renezurbruegg/Demonstrator/3D Modelle/Case/preview.JPG

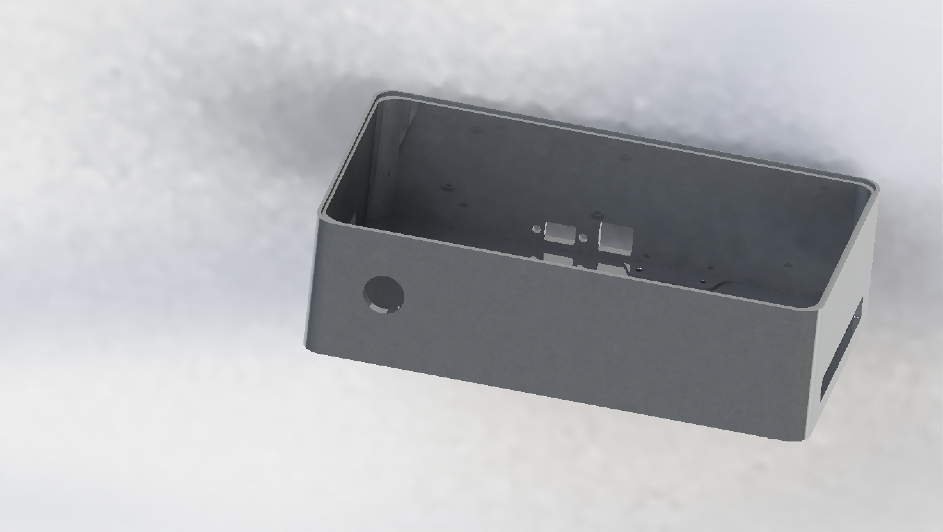
3D Modelle/Case/preview.JPG
