renezurbruegg/Demonstrator/3D Modelle/Case/Mechanical Drawings/Mechanical Drawing 12.PNG

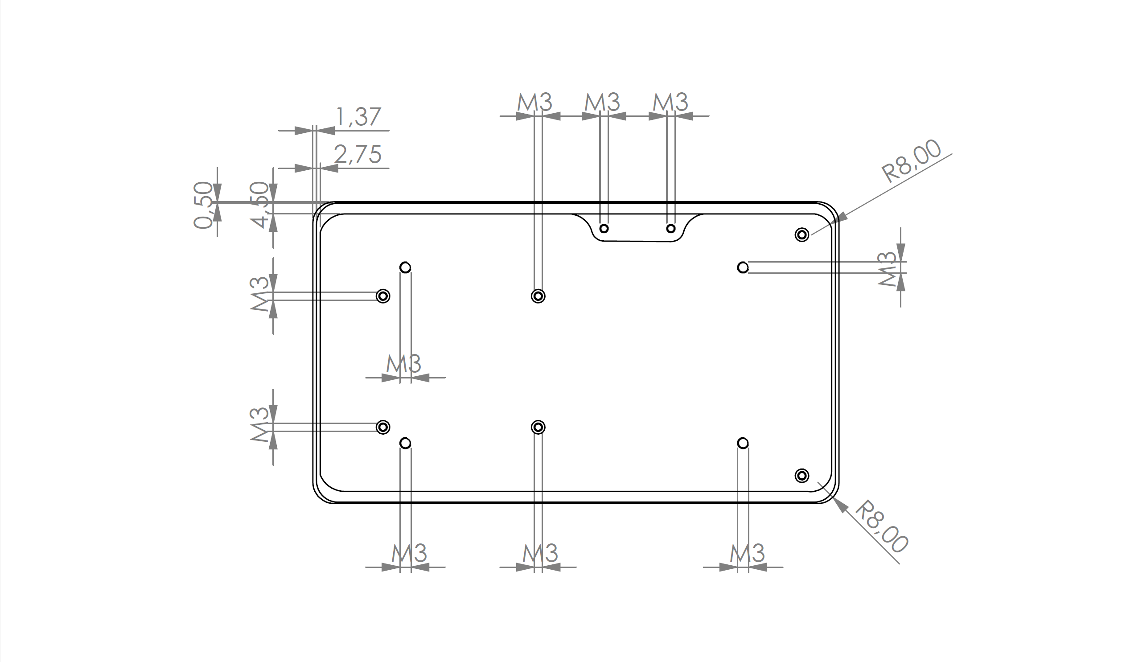
3D Modelle/Case/Mechanical Drawings/Mechanical Drawing 12.PNG
