renezurbruegg/Demonstrator/3D Modelle/Case/Mechanical Drawings/MechanicalDrawing5.PNG

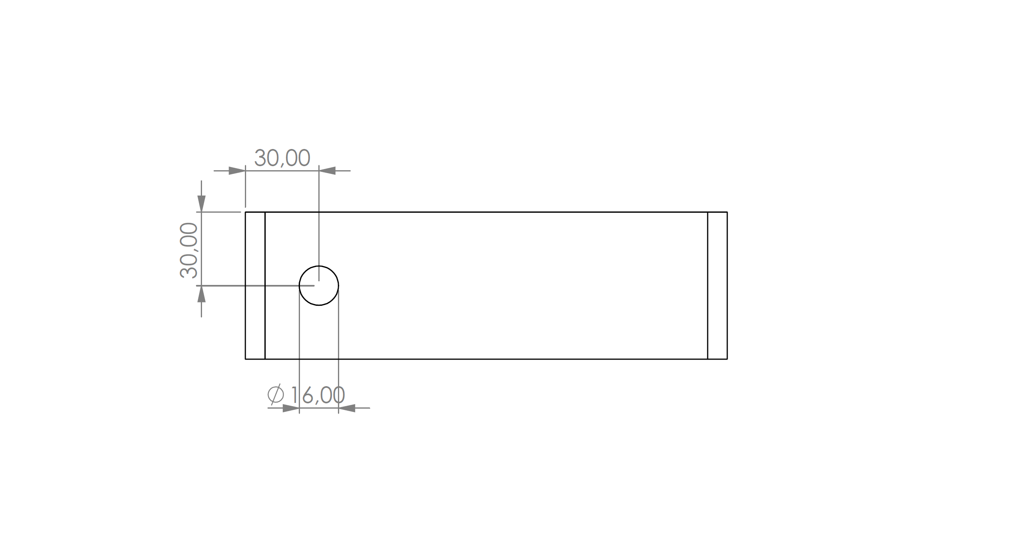
3D Modelle/Case/Mechanical Drawings/MechanicalDrawing5.PNG
