renezurbruegg/Demonstrator/3D Modelle/Case/preview2.JPG

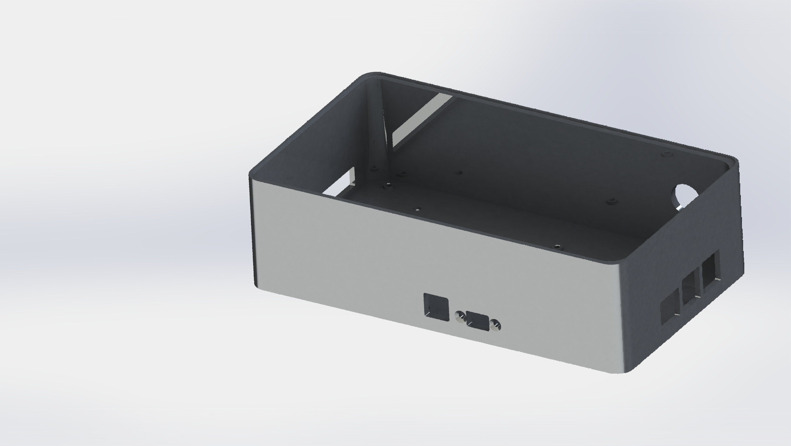
3D Modelle/Case/preview2.JPG
