renezurbruegg/Demonstrator/3D Modelle/Case/pulpdemonstrator.JPG

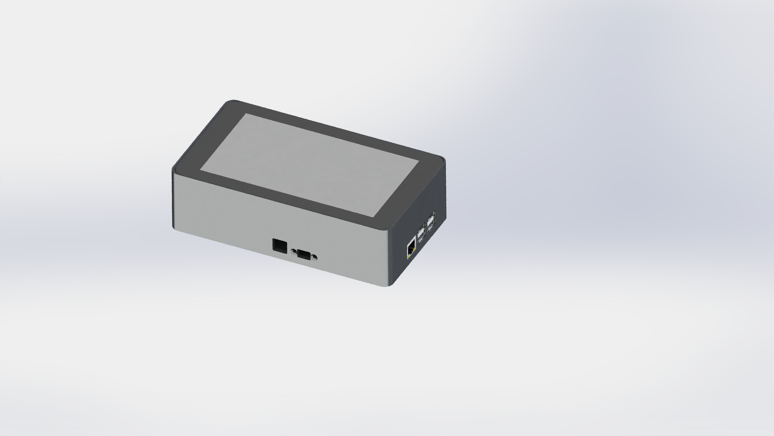
3D Modelle/Case/pulpdemonstrator.JPG
