renezurbruegg/Demonstrator/3D Modelle/Mount/halterunga.JPG

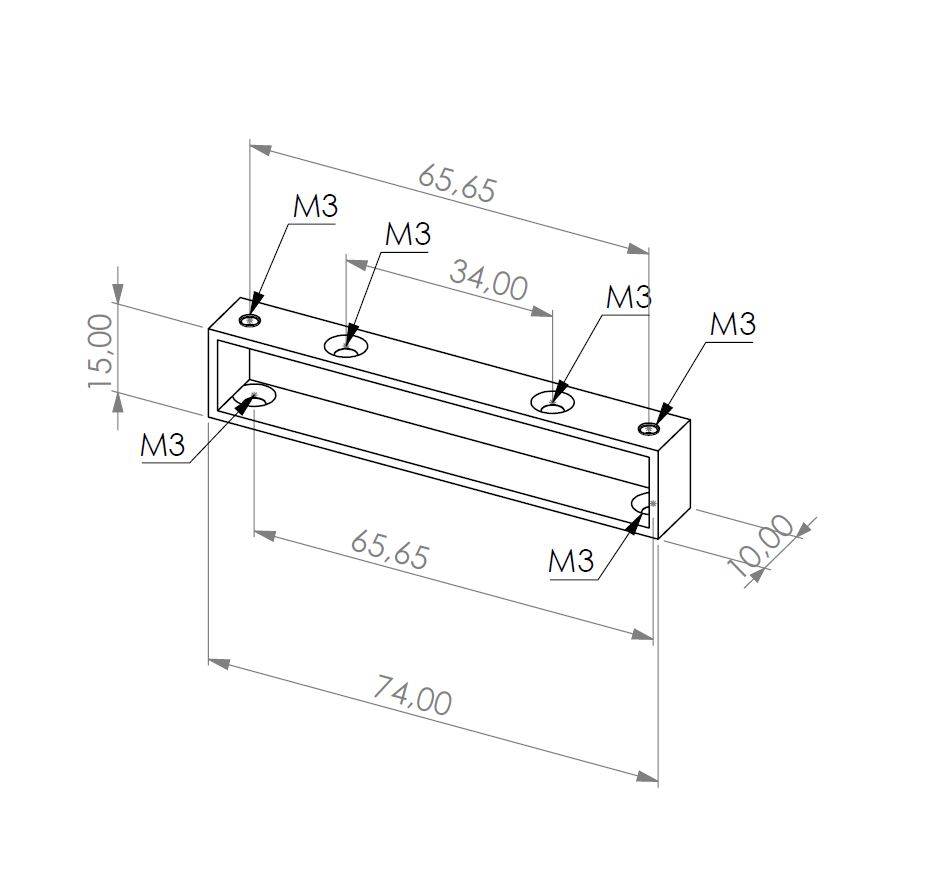
3D Modelle/Mount/halterunga.JPG
