renezurbruegg/Demonstrator/3D Modelle/Mount/halterungb.JPG

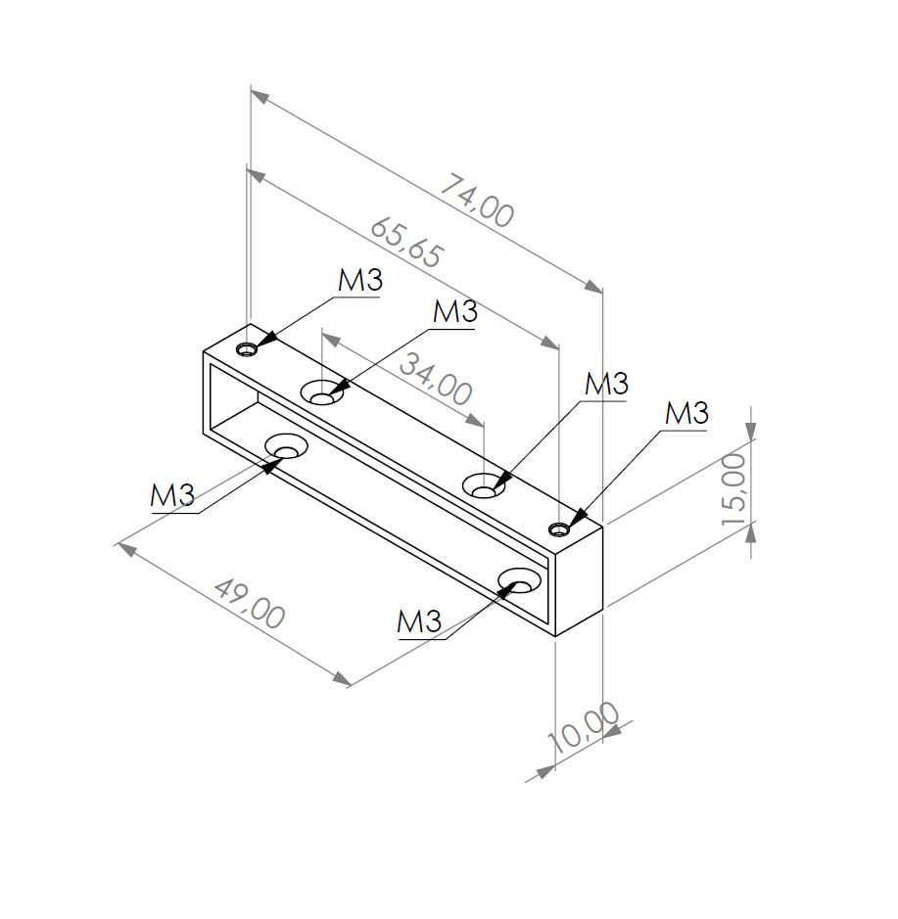
3D Modelle/Mount/halterungb.JPG
