renezurbruegg/Demonstrator/dokumentation/sources/negbodybias.jpg

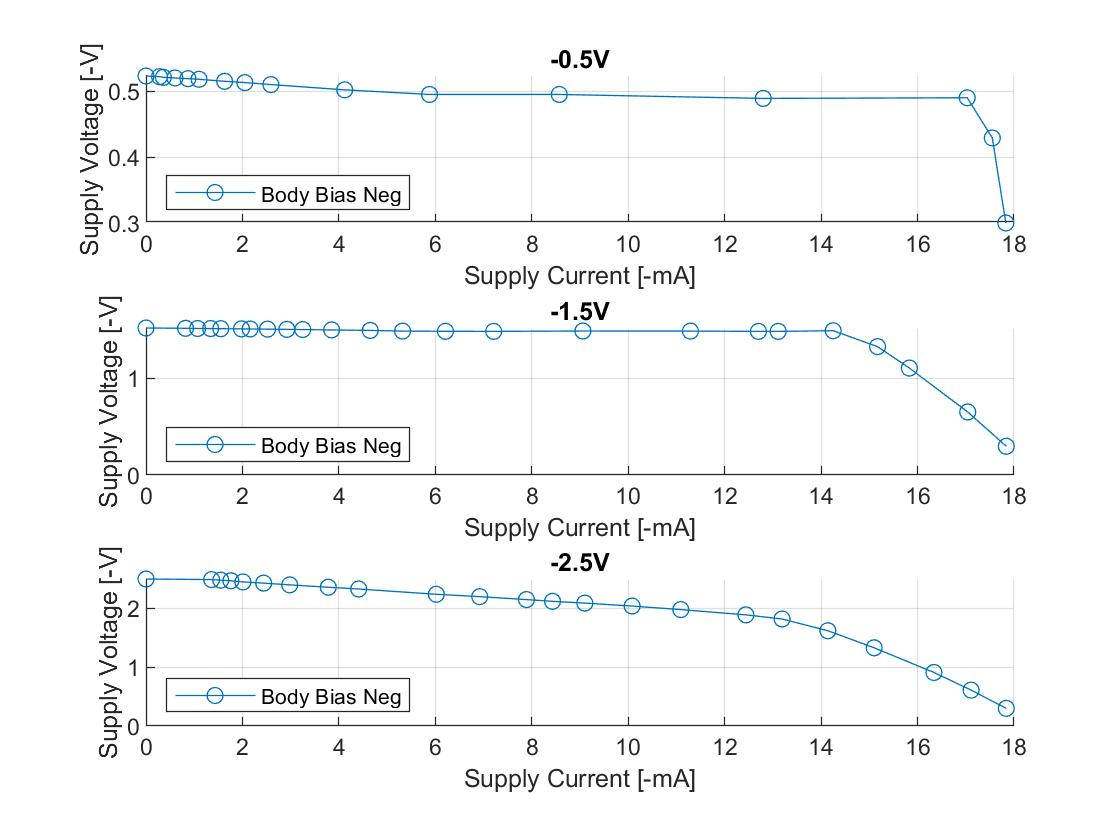
dokumentation/sources/negbodybias.jpg
