renezurbruegg/Demonstrator/dokumentation/sources/posbodybias.jpg

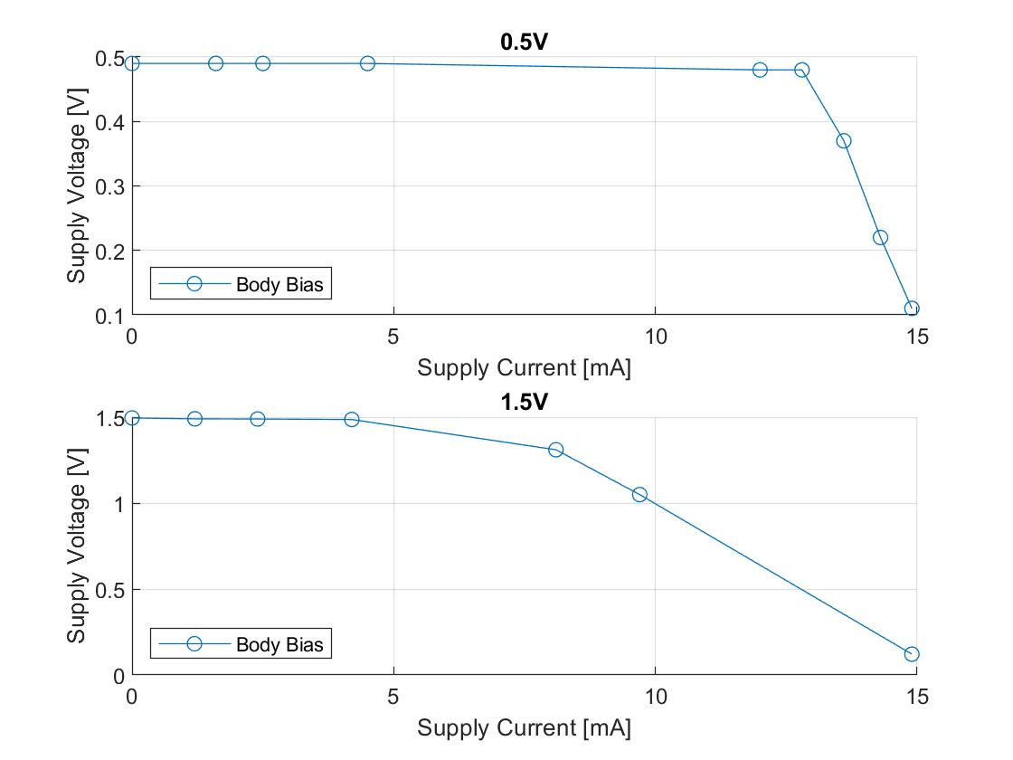
dokumentation/sources/posbodybias.jpg
