renezurbruegg/Demonstrator/dokumentation/sources/precisionall.jpg

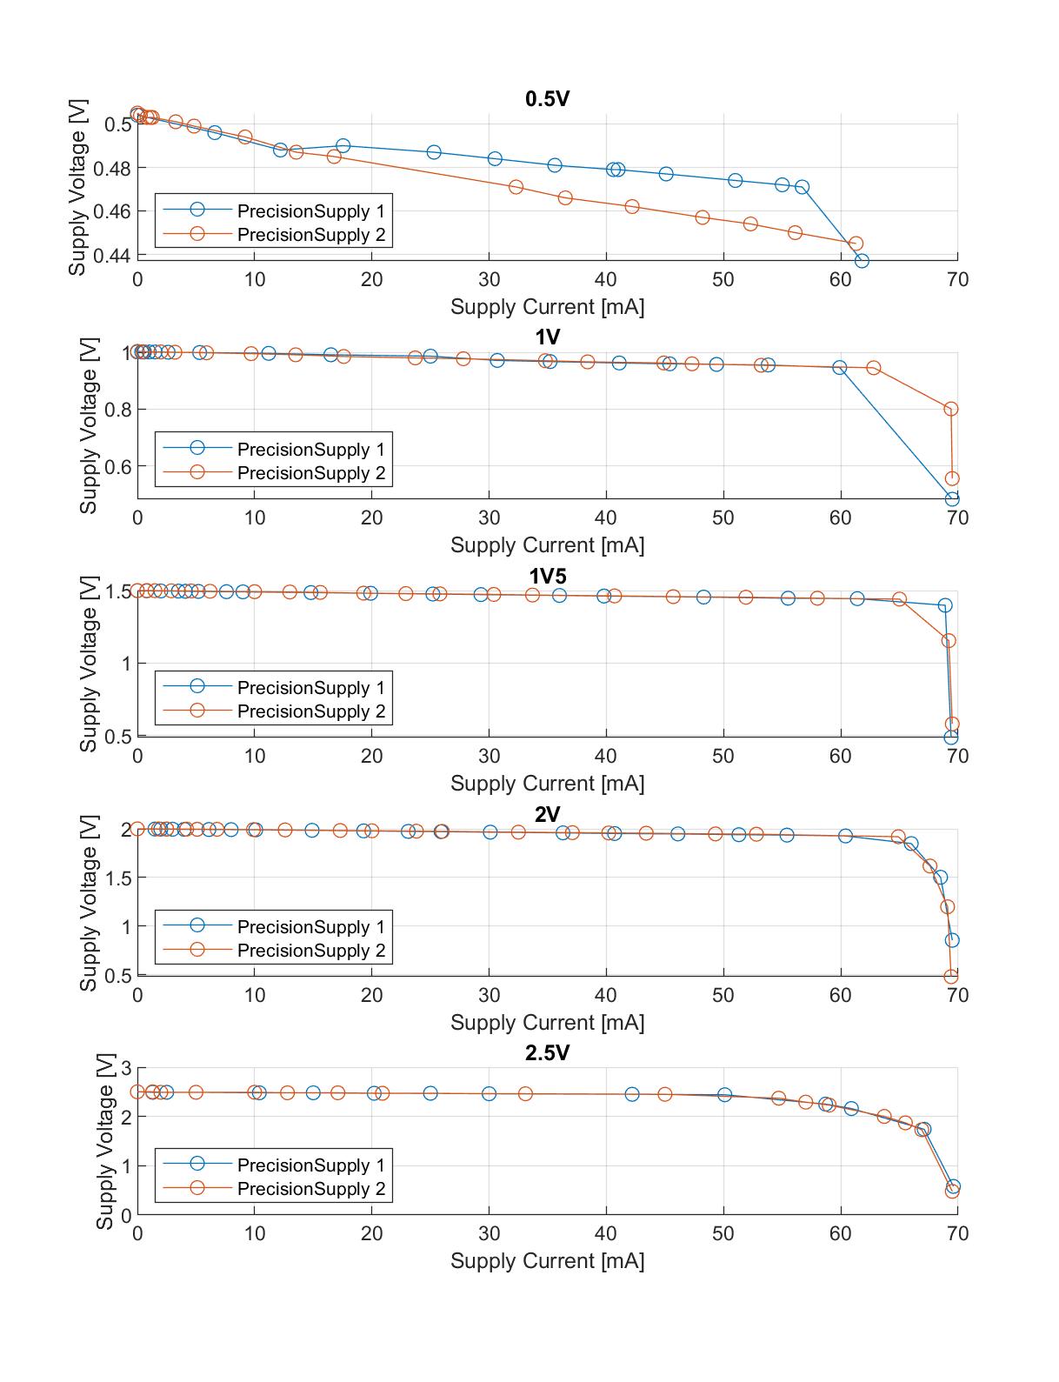
dokumentation/sources/precisionall.jpg
