renezurbruegg/Demonstrator/dokumentation/sources/PrecisionSupply0V.5.jpg

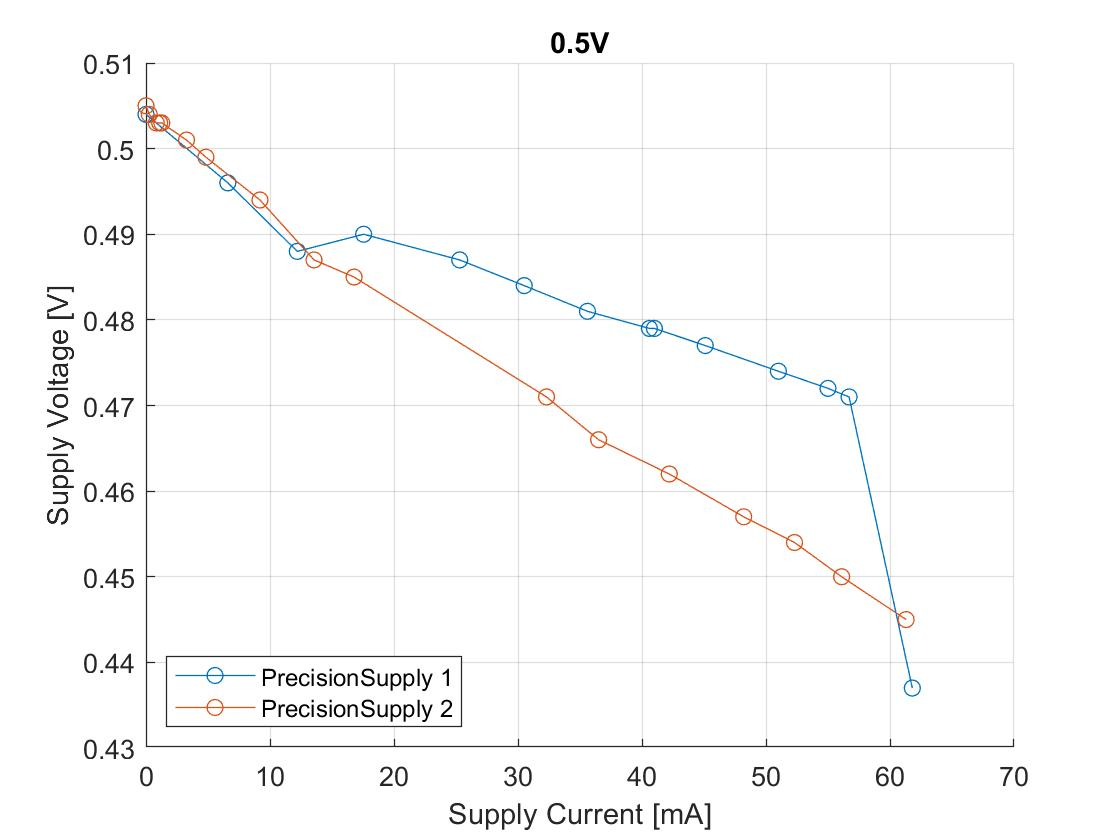
dokumentation/sources/PrecisionSupply0V.5.jpg
