renezurbruegg/Demonstrator/dokumentation/sources/PrecisionSupply1V.5jpg.jpg

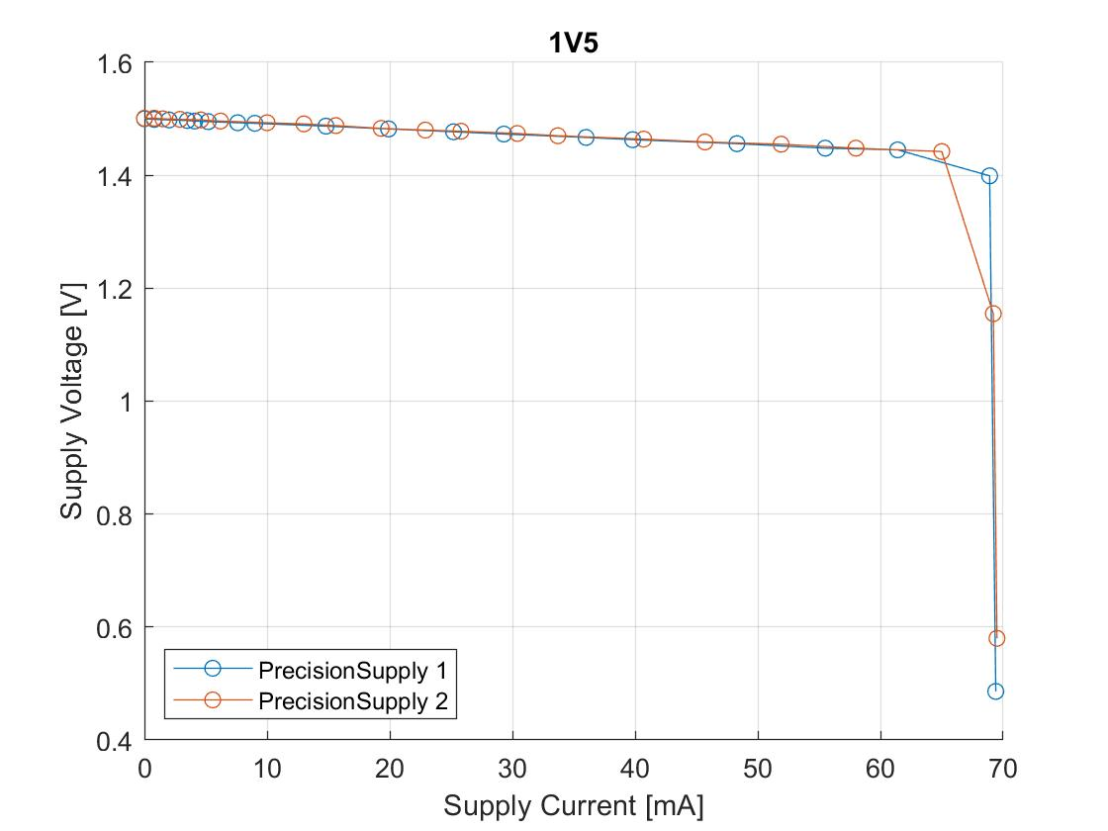
dokumentation/sources/PrecisionSupply1V.5jpg.jpg
