renezurbruegg/Demonstrator/dokumentation/sources/PrecisionSupply1V.jpg

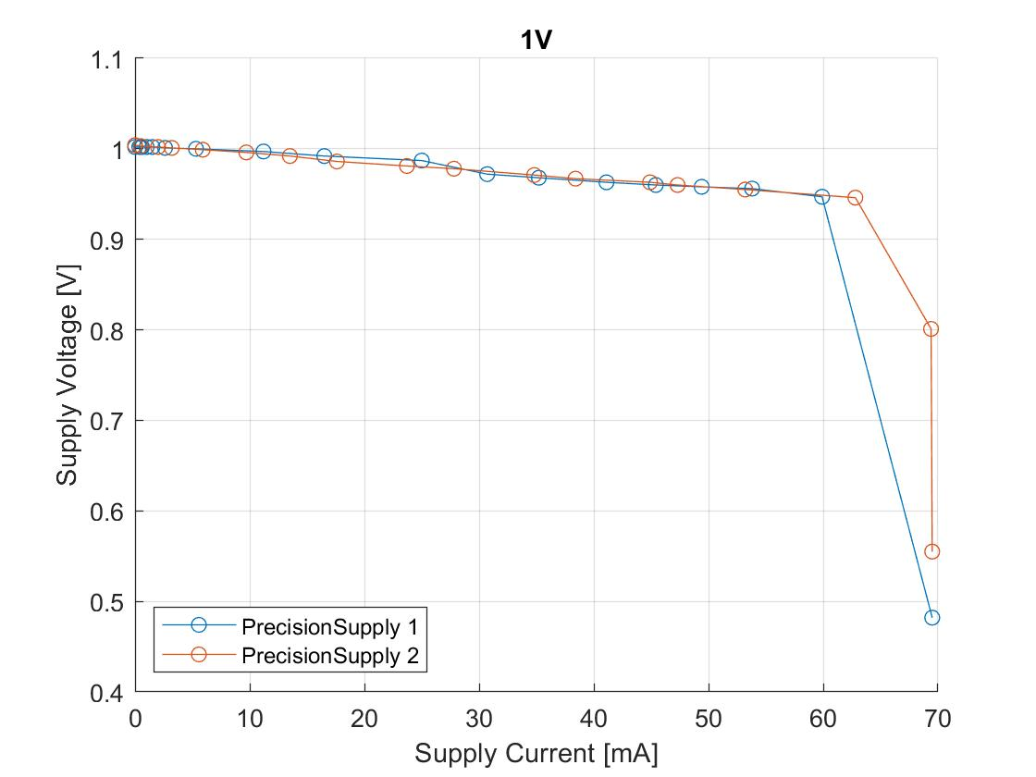
dokumentation/sources/PrecisionSupply1V.jpg
