renezurbruegg/Demonstrator/dokumentation/sources/PrecisionSupply2V5.jpg

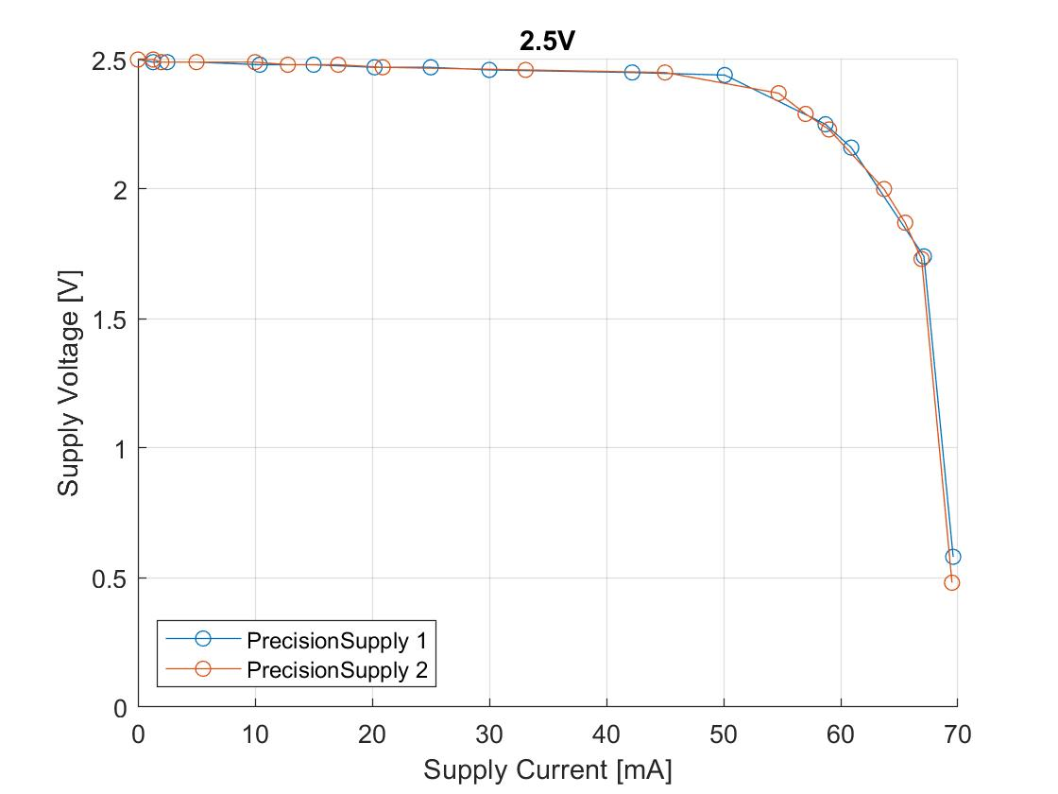
dokumentation/sources/PrecisionSupply2V5.jpg
