renezurbruegg/Demonstrator/dokumentation/sources/PrecisionSupply2V.jpg

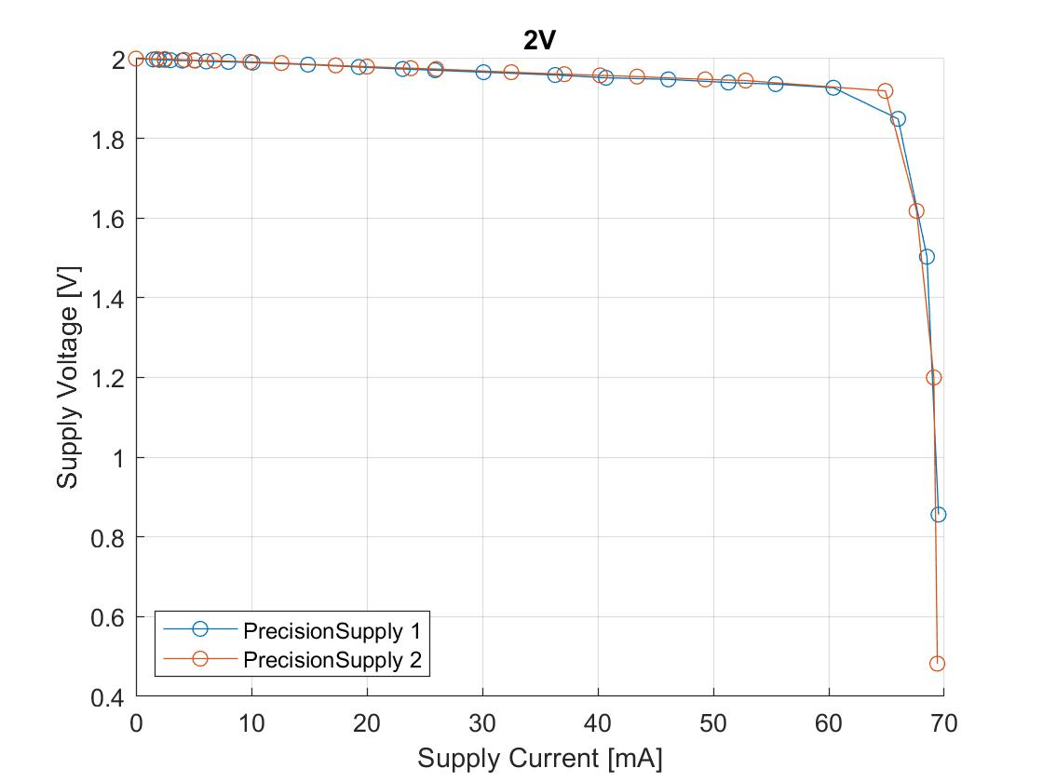
dokumentation/sources/PrecisionSupply2V.jpg
