renezurbruegg/Demonstrator/dokumentation/sources/precisionsupply.jpg

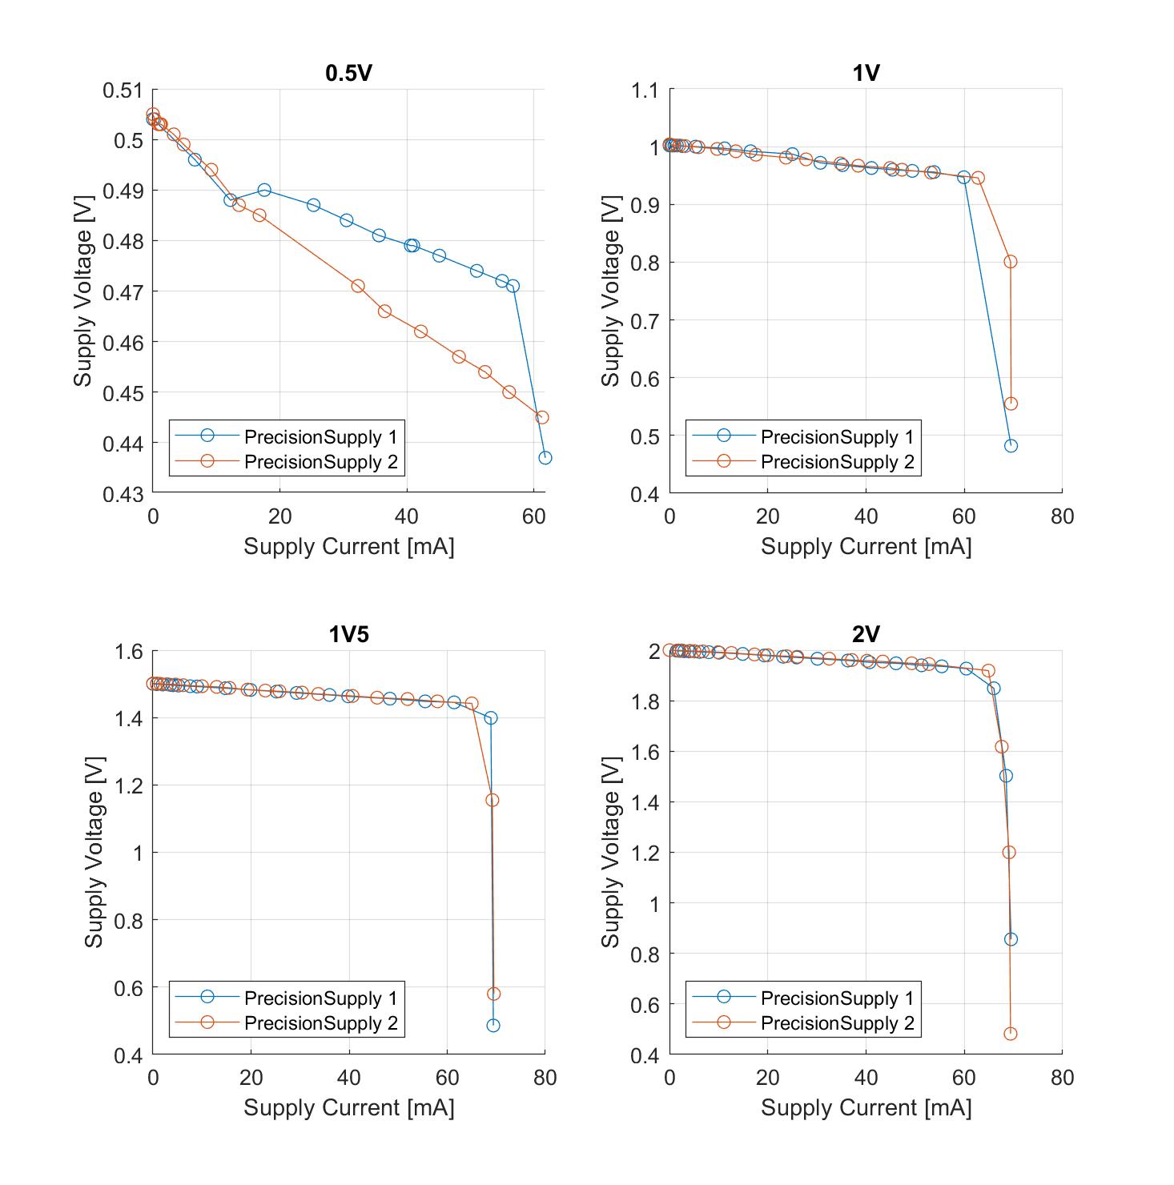
dokumentation/sources/precisionsupply.jpg
