renezurbruegg/Demonstrator/dokumentation/sources/untitled.jpg

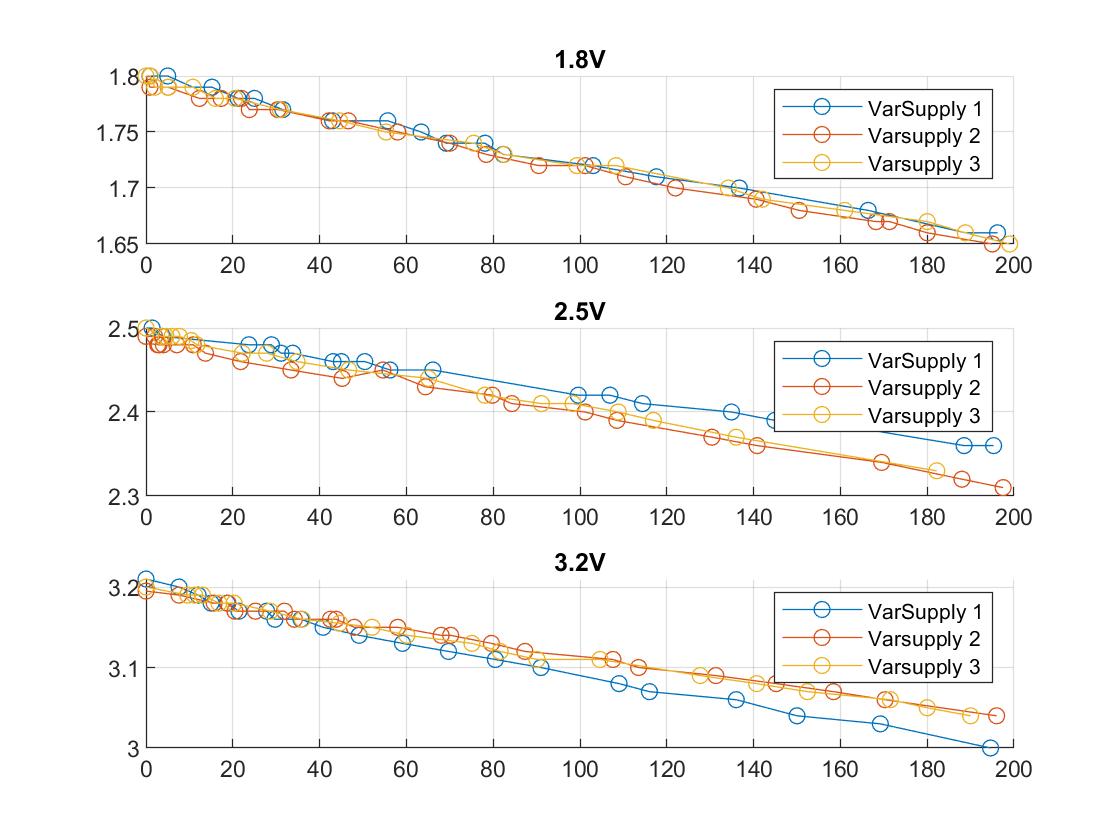
dokumentation/sources/untitled.jpg
