renezurbruegg/Demonstrator/dokumentation/sources/var.jpg

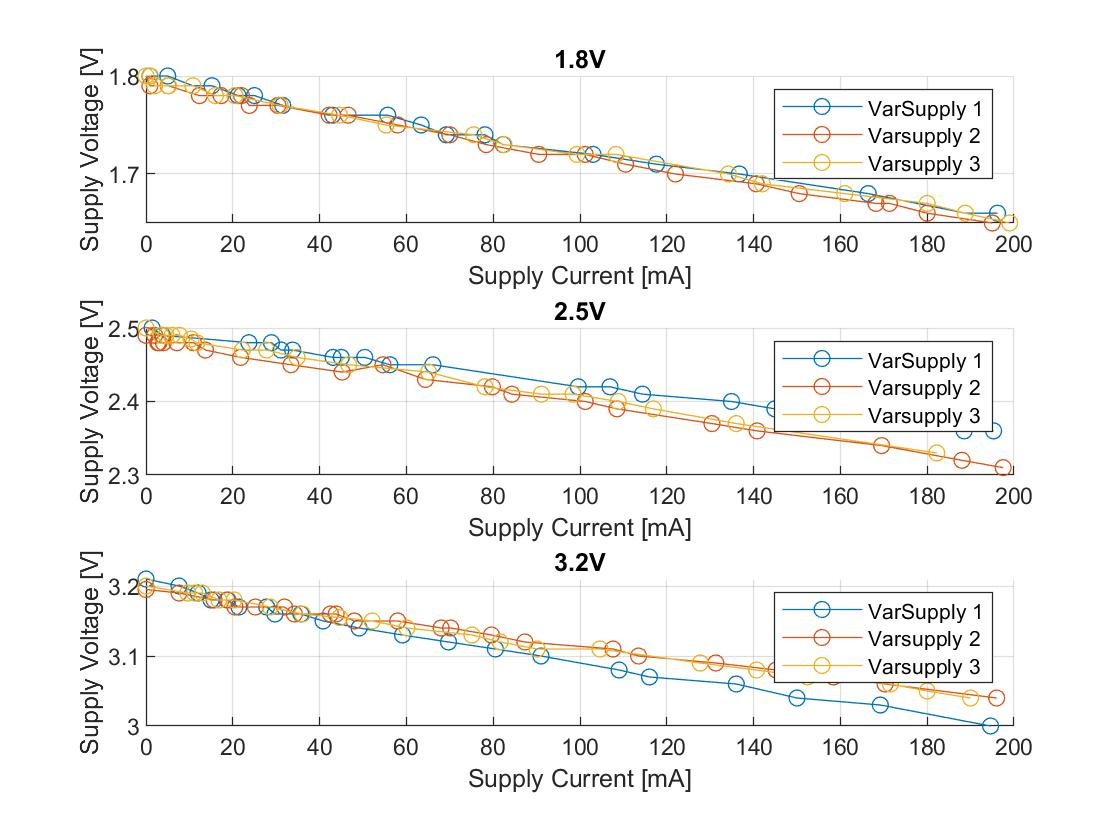
dokumentation/sources/var.jpg
