renezurbruegg/Demonstrator/dokumentation/transientResponse/precision1_2.5V_0.5mA_40mA.png

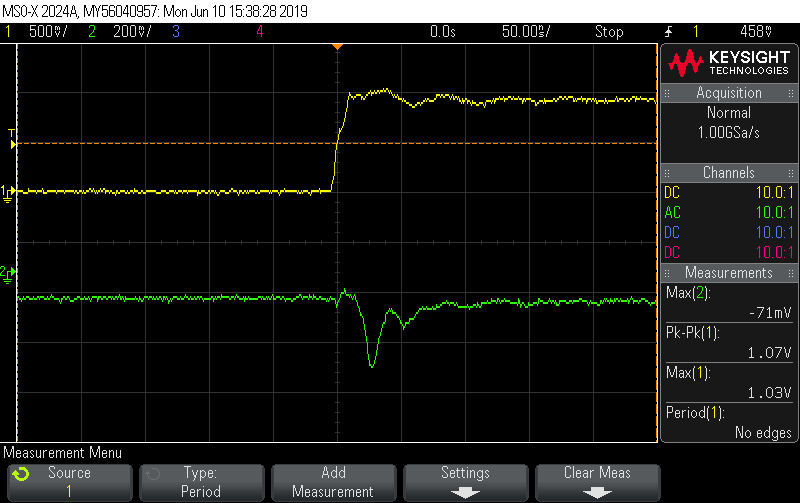
dokumentation/transientResponse/precision1_2.5V_0.5mA_40mA.png
