renezurbruegg/Demonstrator/dokumentation/transientResponse/precision1_2.5V_0.5mA_40mA_falling.png

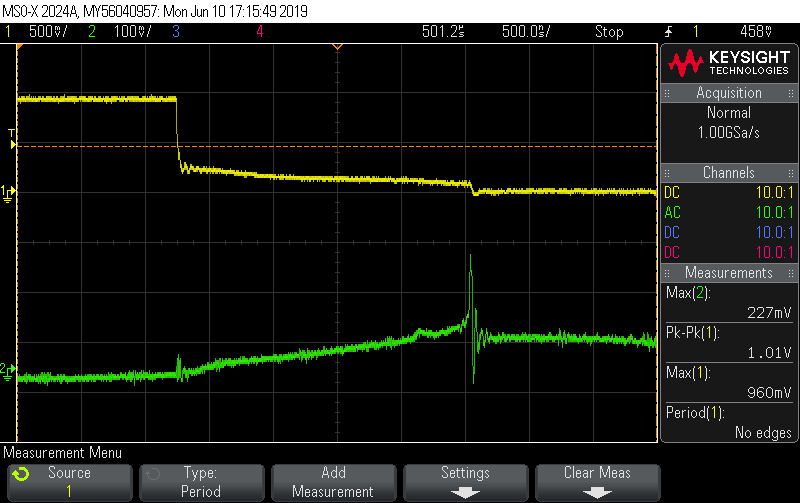
dokumentation/transientResponse/precision1_2.5V_0.5mA_40mA_falling.png
