renezurbruegg/Demonstrator/dokumentation/transientResponse/precision1_2.5V_10mA_40mA.png

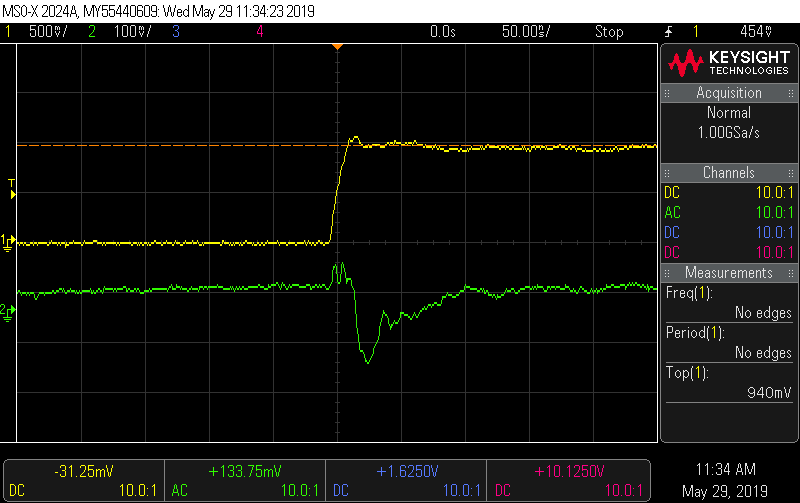
dokumentation/transientResponse/precision1_2.5V_10mA_40mA.png
