renezurbruegg/Demonstrator/dokumentation/transientResponse/precision2_2.5V_10mA_40mA.png

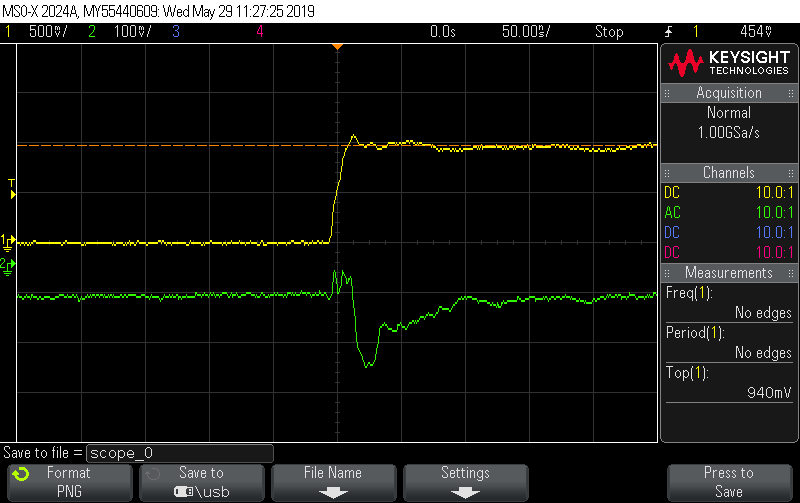
dokumentation/transientResponse/precision2_2.5V_10mA_40mA.png
