renezurbruegg/Demonstrator/dokumentation/transientResponse/PrecisionSupply1fallingedge05mA_40mA.png

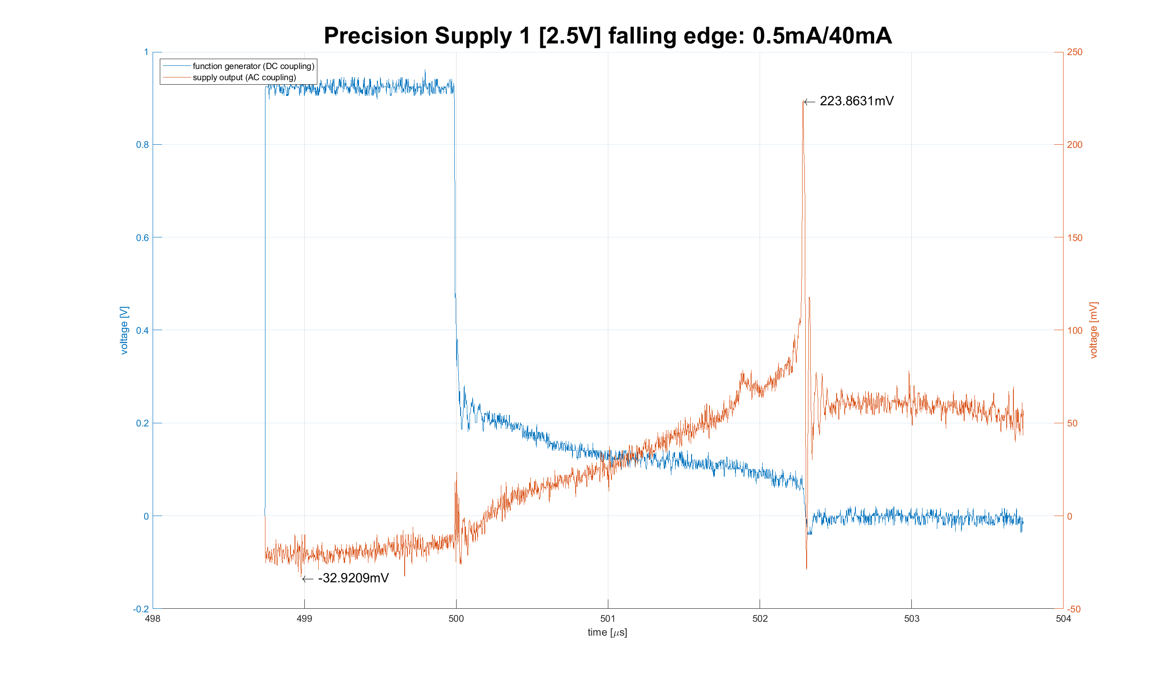
dokumentation/transientResponse/PrecisionSupply1fallingedge05mA_40mA.png
