renezurbruegg/Demonstrator/dokumentation/transientResponse/PrecisionSupply1risingedge05mA_40mA.png

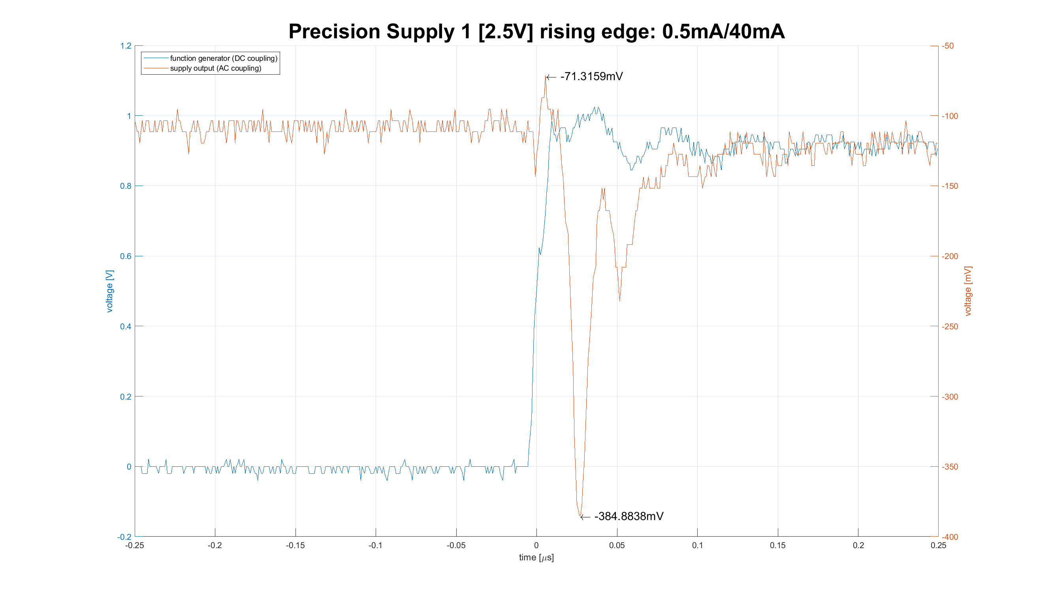
dokumentation/transientResponse/PrecisionSupply1risingedge05mA_40mA.png
