renezurbruegg/Demonstrator/dokumentation/transientResponse/PrecisionSupply1risingedge10mA_40mA.png

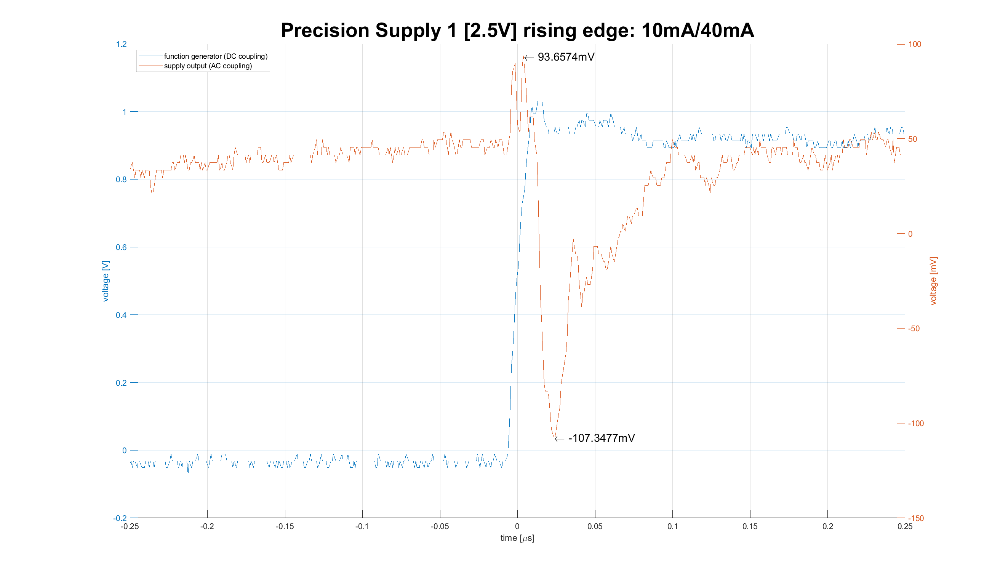
dokumentation/transientResponse/PrecisionSupply1risingedge10mA_40mA.png
