renezurbruegg/Demonstrator/dokumentation/transientResponse/PrecisionSupply2fallingedge05mA_40mA.png

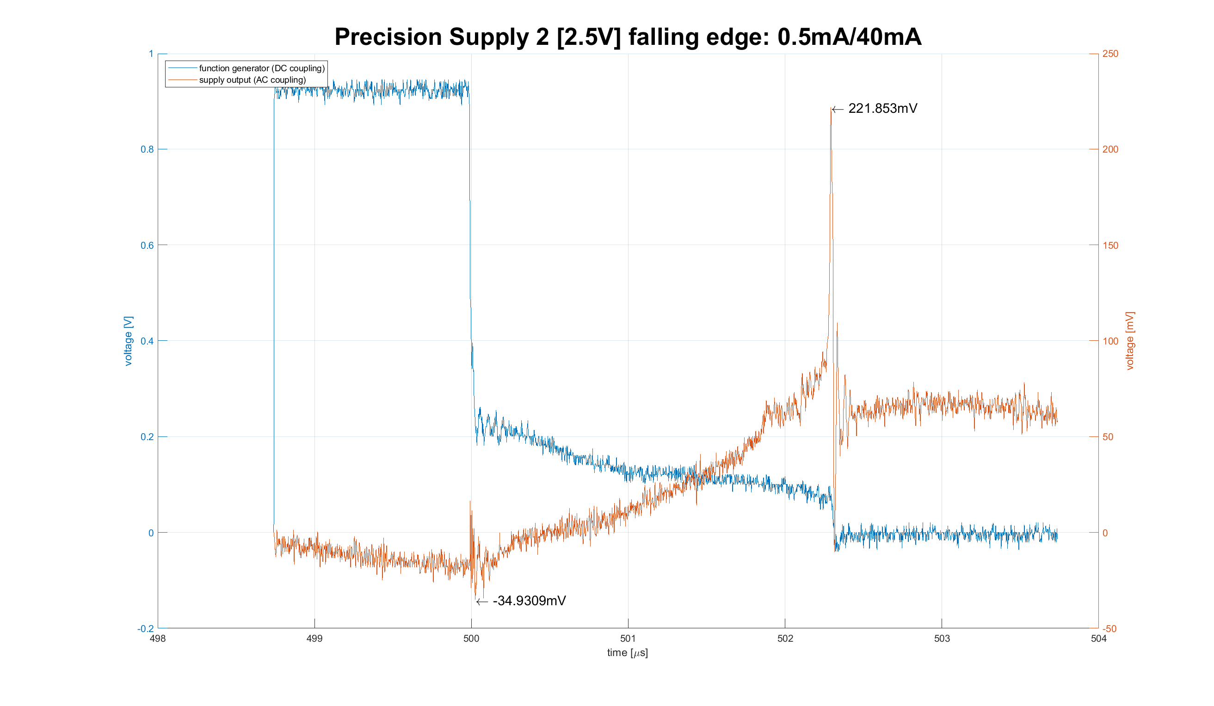
dokumentation/transientResponse/PrecisionSupply2fallingedge05mA_40mA.png
