renezurbruegg/Demonstrator/dokumentation/transientResponse/PrecisionSupply2risingedge05mA_40mA.png

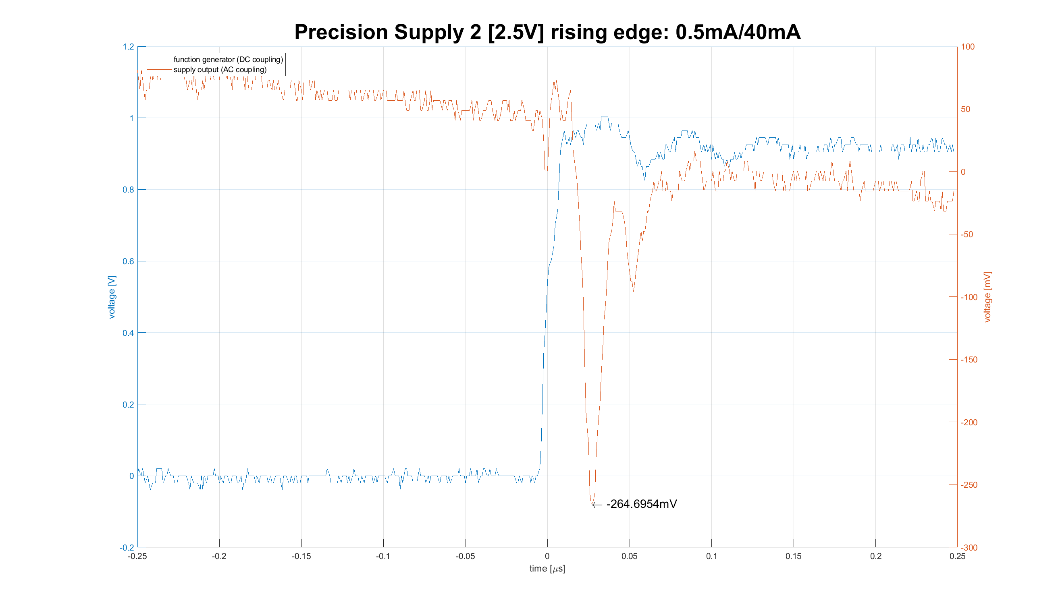
dokumentation/transientResponse/PrecisionSupply2risingedge05mA_40mA.png
