renezurbruegg/Demonstrator/dokumentation/transientResponse/PrecisionSupply2risingedge10mA_40mA.png

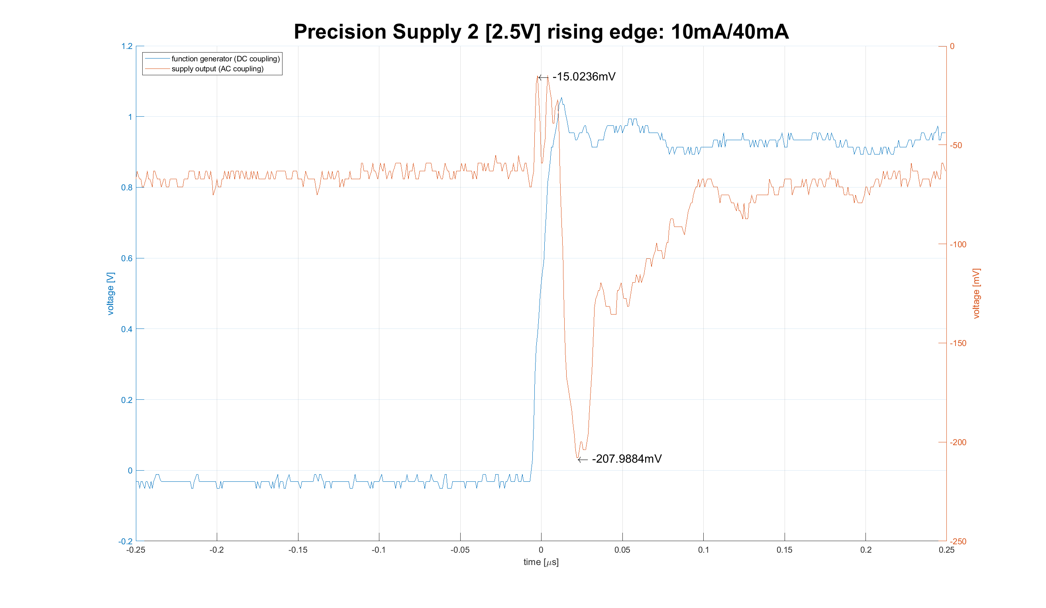
dokumentation/transientResponse/PrecisionSupply2risingedge10mA_40mA.png
