renezurbruegg/Demonstrator/dokumentation/transientResponse/var1_2.5V_0.5mA_100mA.png

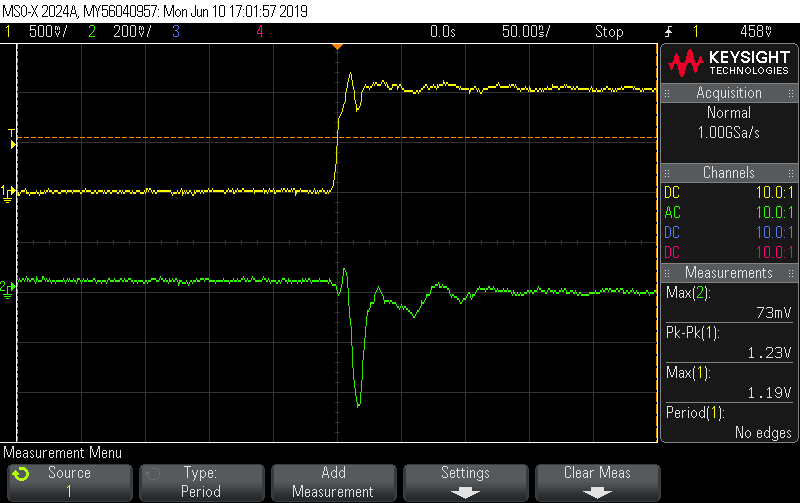
dokumentation/transientResponse/var1_2.5V_0.5mA_100mA.png
