renezurbruegg/Demonstrator/dokumentation/transientResponse/var1_2.5V_10mA_70mA.png

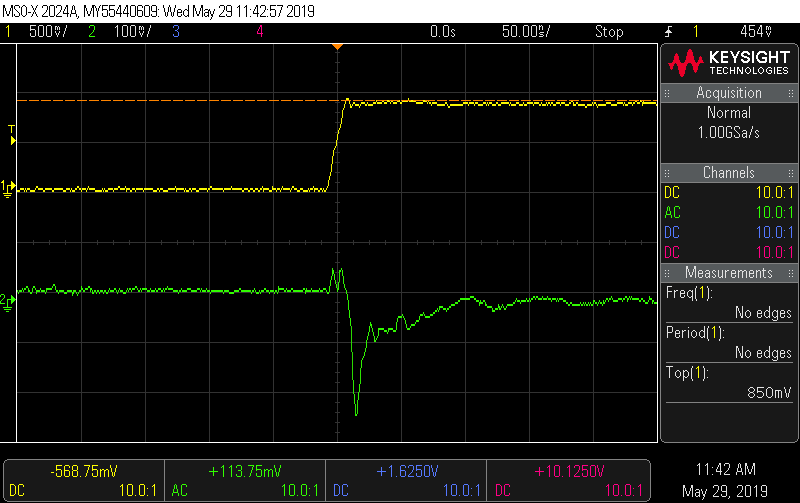
dokumentation/transientResponse/var1_2.5V_10mA_70mA.png
