renezurbruegg/Demonstrator/dokumentation/transientResponse/var2_2.5V_10mA_70mA_falling.png

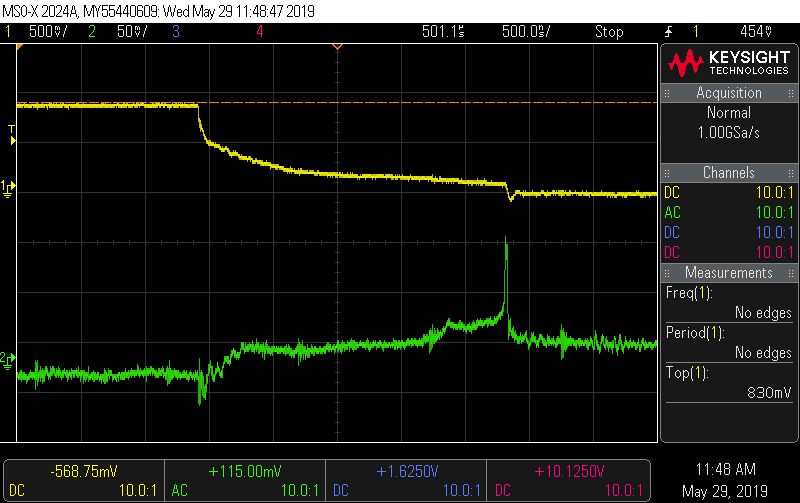
dokumentation/transientResponse/var2_2.5V_10mA_70mA_falling.png
