renezurbruegg/Demonstrator/dokumentation/transientResponse/var3_2.5V_10mA_70mA.png

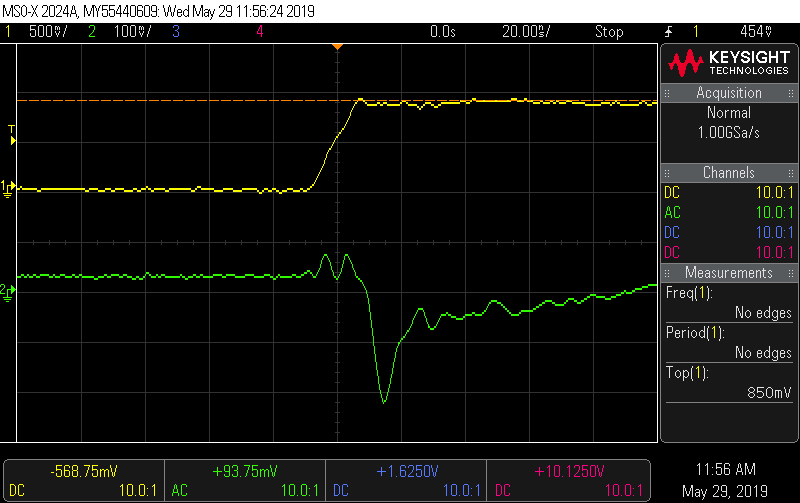
dokumentation/transientResponse/var3_2.5V_10mA_70mA.png
