renezurbruegg/Demonstrator/dokumentation/transientResponse/VariableSupply1fallingedge05mA_100mA.png

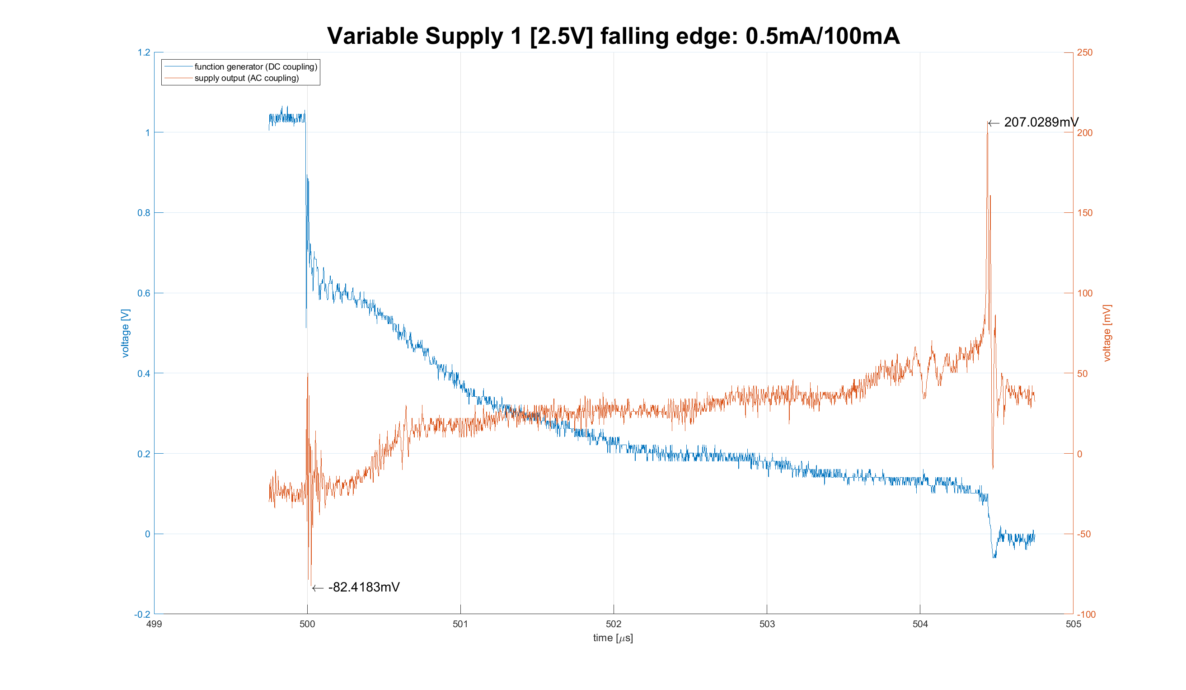
dokumentation/transientResponse/VariableSupply1fallingedge05mA_100mA.png
