renezurbruegg/Demonstrator/dokumentation/transientResponse/VariableSupply1fallingedge10mA_70mA.png

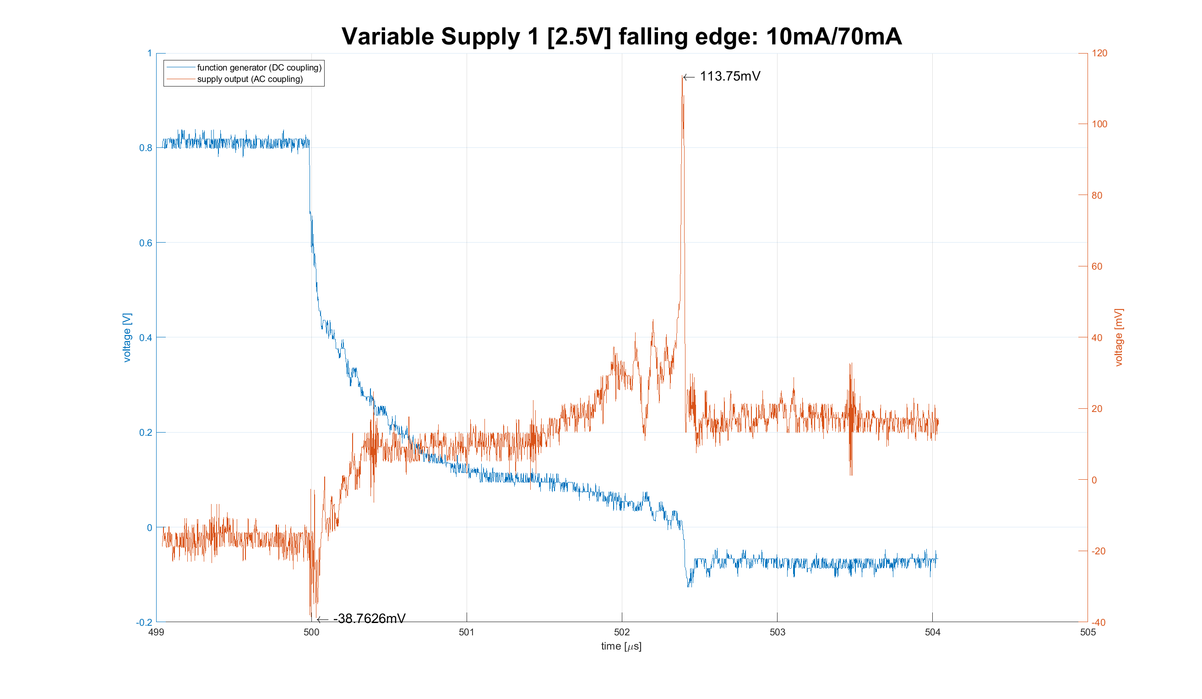
dokumentation/transientResponse/VariableSupply1fallingedge10mA_70mA.png
