renezurbruegg/Demonstrator/dokumentation/transientResponse/VariableSupply1risingedge05mA_100mA.png

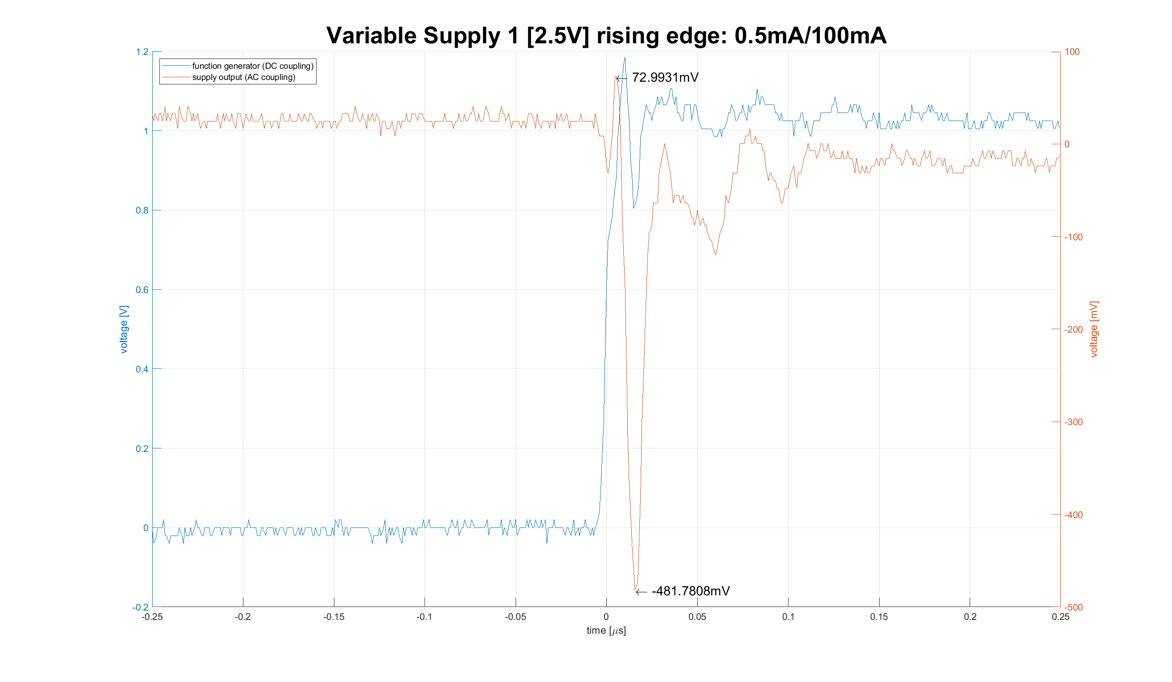
dokumentation/transientResponse/VariableSupply1risingedge05mA_100mA.png
