renezurbruegg/Demonstrator/dokumentation/transientResponse/VariableSupply1risingedge10mA_70mA.png

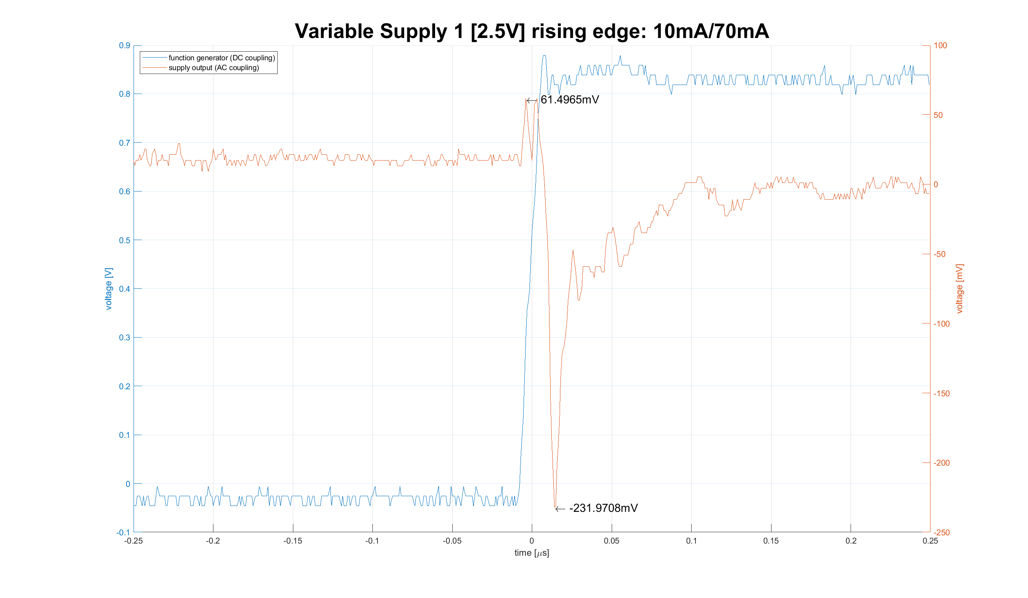
dokumentation/transientResponse/VariableSupply1risingedge10mA_70mA.png
