renezurbruegg/Demonstrator/dokumentation/transientResponse/VariableSupply2fallingedge10mA_70mA.png

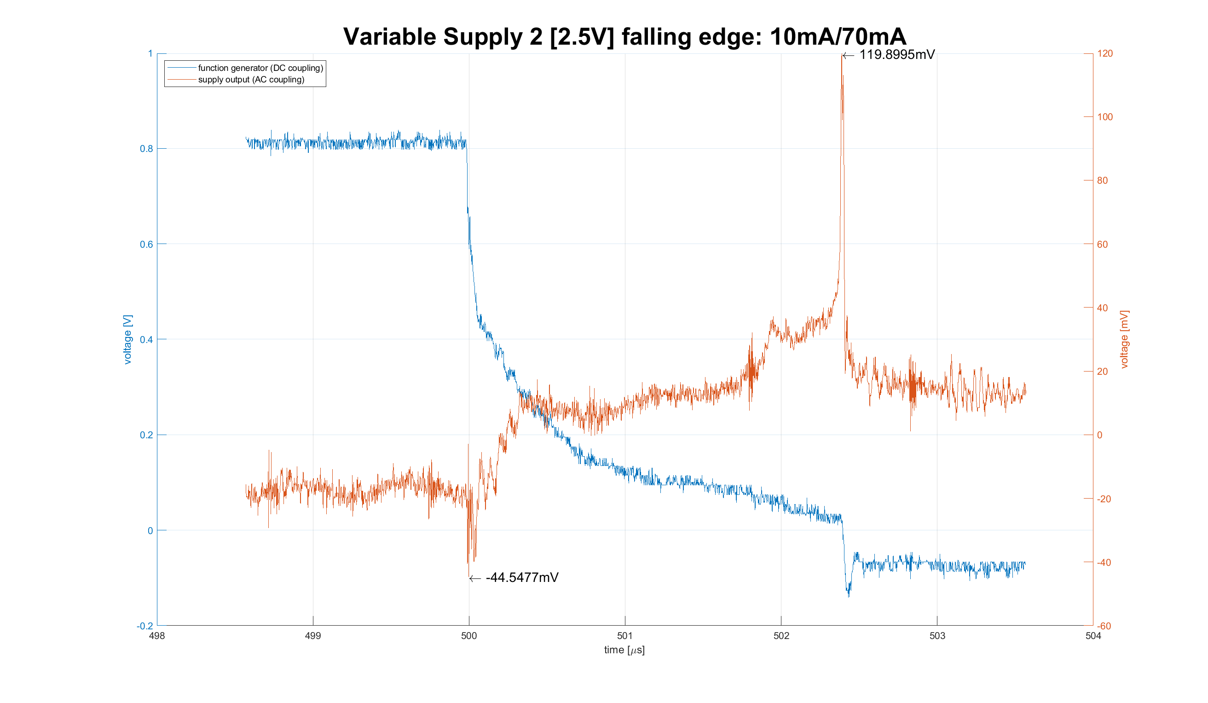
dokumentation/transientResponse/VariableSupply2fallingedge10mA_70mA.png
