renezurbruegg/Demonstrator/dokumentation/transientResponse/VariableSupply2risingedge05mA_100mA.png

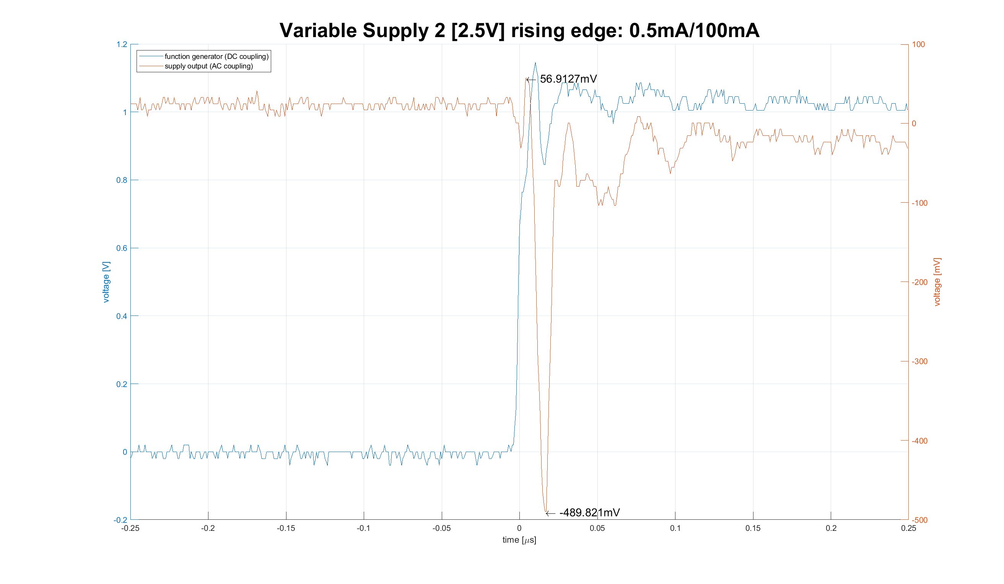
dokumentation/transientResponse/VariableSupply2risingedge05mA_100mA.png
