renezurbruegg/Demonstrator/dokumentation/transientResponse/VariableSupply2risingedge10mA_70mA.png

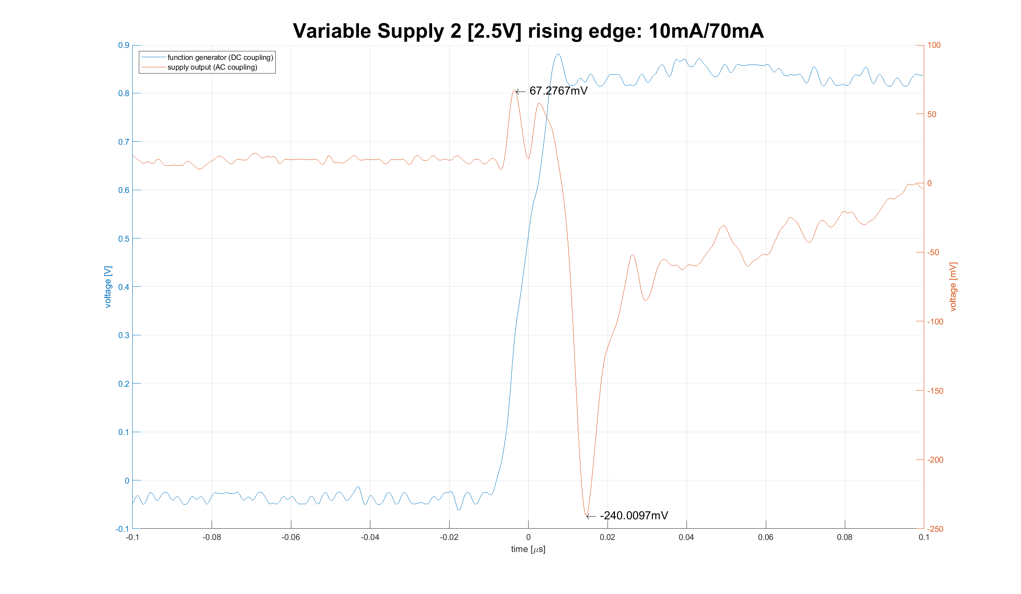
dokumentation/transientResponse/VariableSupply2risingedge10mA_70mA.png
