renezurbruegg/Demonstrator/dokumentation/transientResponse/VariableSupply3fallingedge10mA_70mA.png

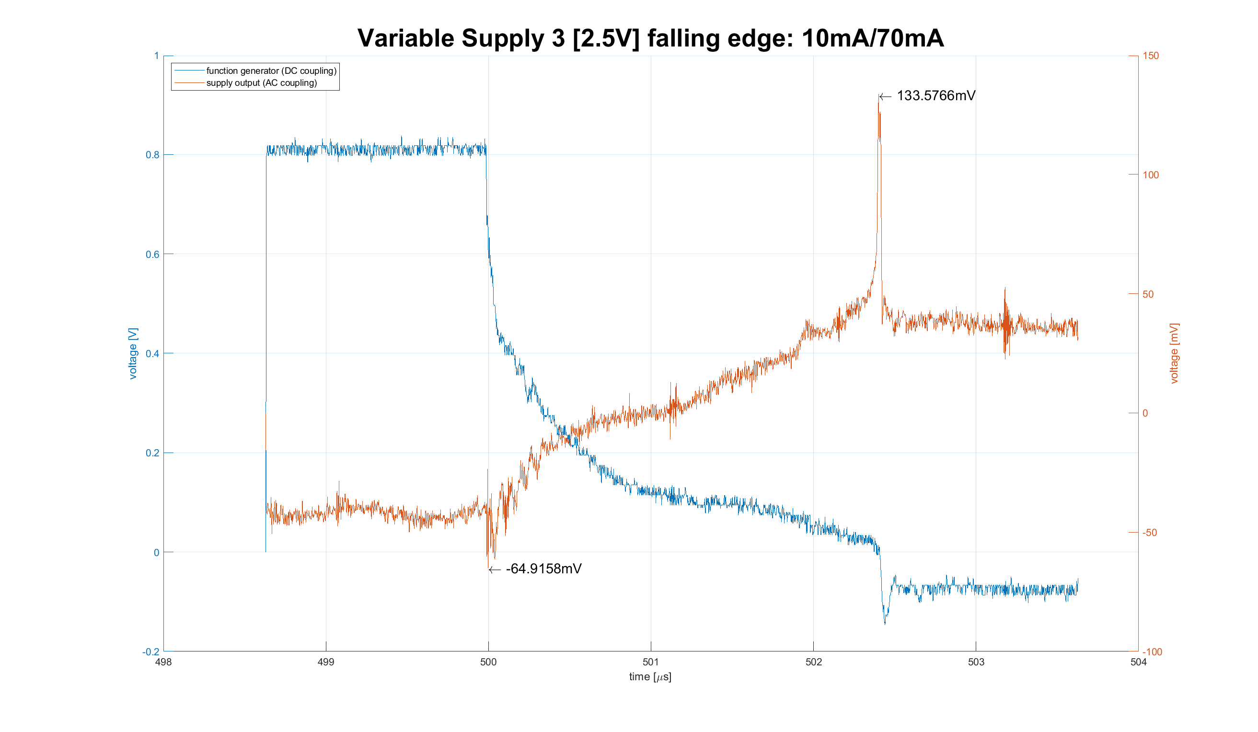
dokumentation/transientResponse/VariableSupply3fallingedge10mA_70mA.png
