renezurbruegg/Demonstrator/dokumentation/transientResponse/VariableSupply3risingedge05mA_100mA.png

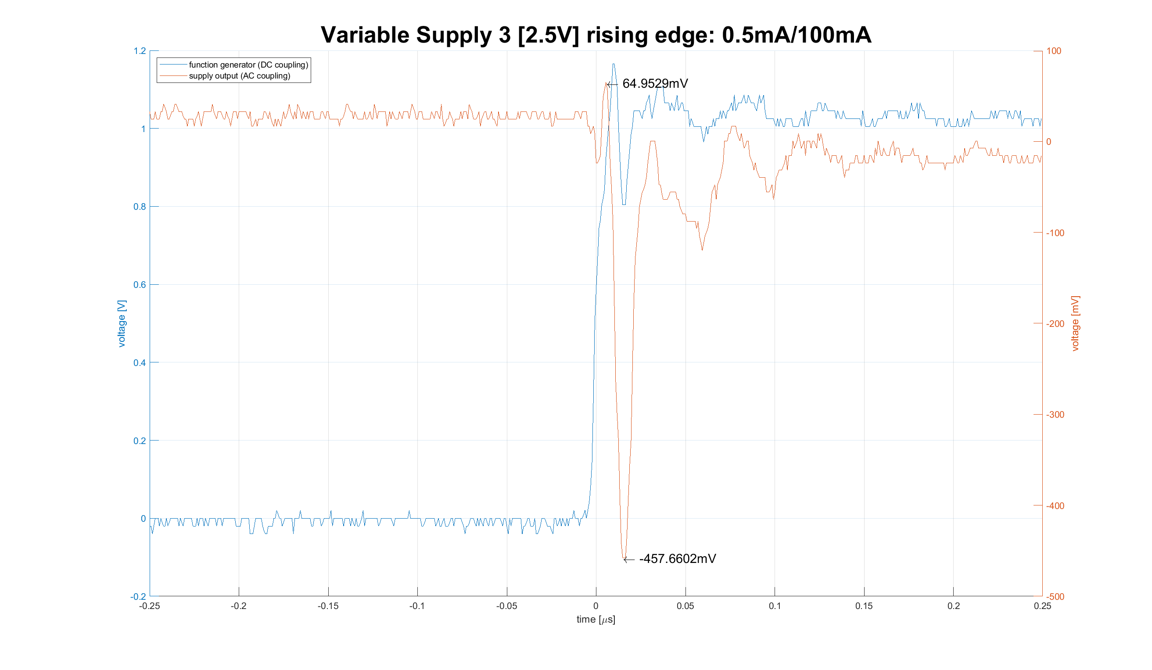
dokumentation/transientResponse/VariableSupply3risingedge05mA_100mA.png
