renezurbruegg/Demonstrator/dokumentation/measurements/current/meas_CM3_19.9994_mA.csv

cm3
20.533077261233988
20.68565029035561
20.53222010938499
20.608506623945804
20.582792068475865
20.41221885052529
20.359075435887423
20.747365223483456
20.44307631708921
20.60593516839881
20.49364827618009
20.624792509076762
20.372789865471386
20.555363209307934
20.501362642821068
20.399361572790323
20.591363586965844
20.49364827618009
20.643649849754716
20.78679420853736
20.546791690817955
20.399361572790323
20.53222010938499
20.604220864700814
20.4885053650861
20.58107776477787
20.675364468167636
20.72165066801352
20.258788669554672
20.622221053529767
20.680507379261623
20.517648527952026
20.619649597982775
20.32393221007851
20.511648465009042
20.554506057458937
20.567363335193903
20.606792320247806
20.426790431958253
20.620506749831772
20.46793372071015
20.341075247058466
20.508219857613053
20.4885053650861
20.528791501989
20.539934476025973
20.662507190432667
20.682221682959618
20.74993667903045
20.52450574274401
20.689078897751603
20.662507190432667
20.4893625169351
20.577649157381877
20.413933154223287
20.648792760848703
20.457647898522175
20.691650353298595
20.385647143206356
20.382218535810363
20.527077198291003
20.337646639662474
20.665078645979662
20.515934224254032
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
