renezurbruegg/Demonstrator/dokumentation/measurements/current/meas_CM3_199.996_uA.csv

cm3
203.26561688336858
195.48580357989184
204.7205670783011
196.7044402081315
188.96632929877697
200.85614522297078
197.94161123375883
204.6232614920158
200.97661880599068
205.95310450458152
199.14634706395773
196.9314865761305
200.5688620634618
202.12111784467962
204.70203268091342
198.71078872534736
193.4840886620229
195.0039092478123
199.3131566404468
203.13587610165484
200.38815168893197
197.55702248796456
196.95928817221204
204.33597833250684
200.04526533726
201.7457962975792
203.64557202981592
201.1758635779082
206.91689316874064
198.83126230836726
198.60421594036822
202.13501864272038
198.92856789465253
195.03634444324072
207.8714146342059
202.20452263292415
203.66874002655052
201.643857111947
200.72640444125705
201.300970760275
189.08680288179687
207.56096347796236
198.68762072861276
203.6872744239382
196.94075377482437
196.4588594427448
200.97661880599068
199.13244626591697
196.19011068062352
201.33803955505033
196.2318130747458
194.46177812422277
198.90539989791796
201.92650667210904
202.51497378916773
205.31830139405363
201.3241387570096
202.19062183488342
199.44289742216054
194.08182297777543
203.09417370753258
201.56508592304937
193.29411108879924
200.60593085823717
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
