renezurbruegg/Demonstrator/dokumentation/measurements/current/meas_CM3_299.994_uA.csv

cm3
288.6860208438174
301.7203358067002
295.7985958413379
297.5639971925139
296.86432369112924
287.9261105509227
301.70643500865935
302.1327261485759
307.79961814985774
294.37608084183375
306.6782871079034
302.1651613440044
300.0059040483402
300.4090271915221
296.3824293590497
307.4196630034104
306.82192868765776
292.85162665669753
302.5960860832678
299.84372807119803
303.4069659689786
300.6314399601742
302.55901728849244
302.415375708738
305.10286332995094
293.565200956123
303.0733468160005
297.59179878859544
293.5188649626538
298.5046178599385
290.8174765434001
294.52435602093516
291.9341739860076
289.2096175700193
302.46634530155404
301.3913502530689
299.99200325029943
311.53893282282115
290.50239178780964
295.4510758903189
300.79824953666326
298.6853282344683
305.895208818274
302.84166684865454
300.6777759536434
295.13599113472844
298.16173150826654
293.5559337574292
297.2906148310458
300.6916767516842
291.52641724347876
295.3537703040337
294.81163918044416
300.4970655791136
307.2343190295336
293.3010857933486
297.2998820297396
292.64774828543307
304.83411456782966
306.14078958366076
307.9942293224283
299.8576288692388
307.5679381825118
305.54768886725515
292.1287851585782
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
