renezurbruegg/Demonstrator/dokumentation/measurements/current/meas_CM3_30.0003_mA.csv

cm3
30.921757671088187
30.88061438233629
30.77175609751356
30.966329567236077
30.776899008607547
30.842042549131385
30.870328560148316
30.746041542043624
30.769184641966564
30.810327930718465
30.668897875633814
30.974043933877056
31.01690152632695
30.986901211612025
31.01690152632695
30.78289907155053
31.016044374477953
30.866042800903326
30.850614067621365
30.721184138422686
30.794042045587503
30.82747096769842
30.904614634108228
30.92518627848418
30.986901211612025
30.790613438191514
30.89261450822226
30.793184893738506
31.039187474400894
30.666326420086822
30.844614004678377
30.851471219470362
30.90032887486324
30.88061438233629
30.750327301288614
30.85918558611134
30.842042549131385
30.933757796974156
30.772613249362557
30.753755908684603
30.918329063692195
30.861757041658336
30.893471660071256
30.830899575094413
30.983472604216033
30.974043933877056
30.993758426404007
30.935472100672154
30.84804261207437
30.656040597898848
30.987758363461023
30.74347008649663
30.701469645895735
30.86347134535633
30.7151840754797
30.753755908684603
30.76747033826857
30.500038961381236
30.967186719085074
30.85918558611134
30.981758300518038
30.90032887486324
30.96804387093407
30.890043052675267
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
