renezurbruegg/Demonstrator/dokumentation/measurements/voltage/voltagemeasurement150mVrange.png

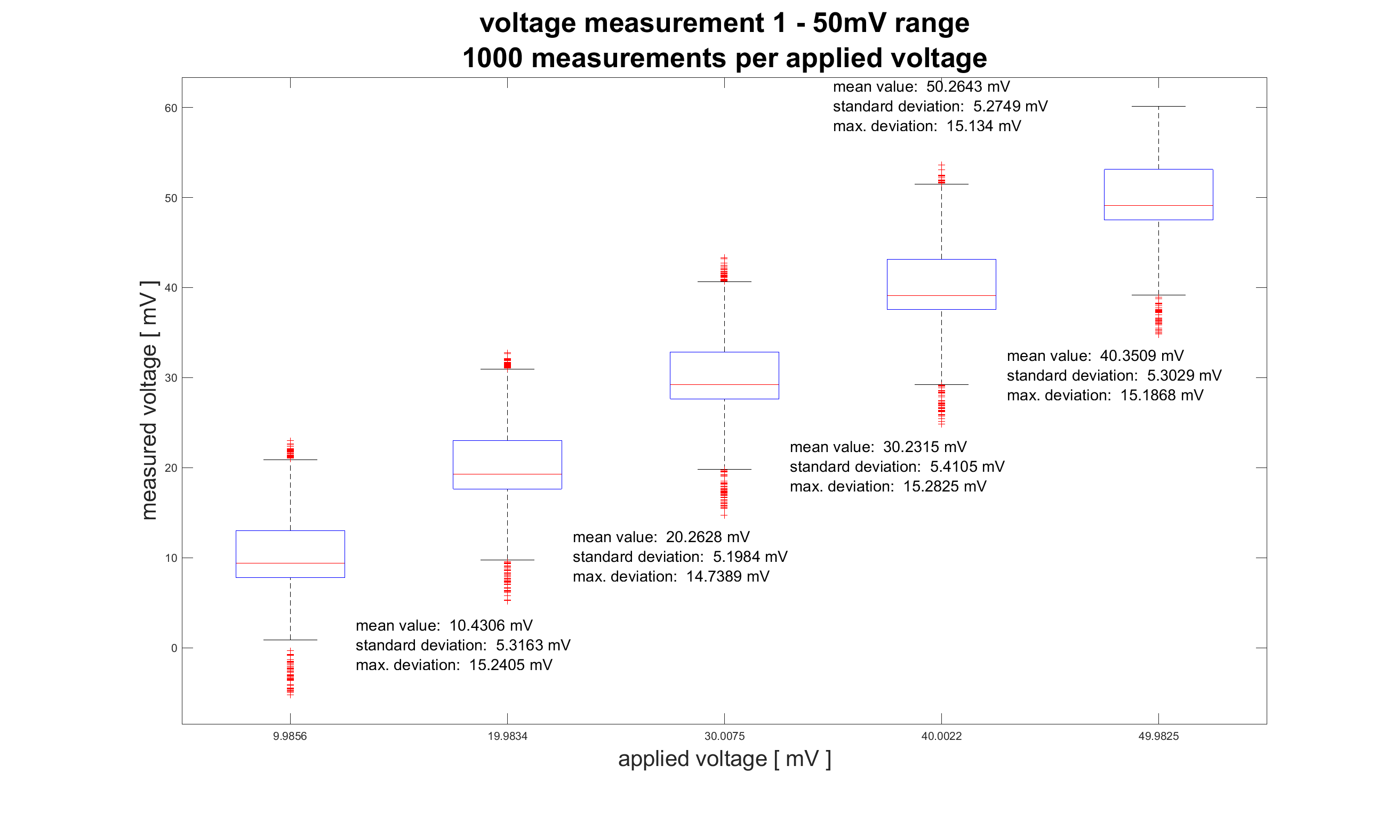
dokumentation/measurements/voltage/voltagemeasurement150mVrange.png
